hansliss/HexKeyboard/Sketch/HexKeyboard/KeyboardLib.cpp

#include <HID.h>
#include <string.h>
#include "KeyboardLib.h"

const uint8_t REPORT_ID = 0x02;
/*
static const uint8_t hidReportDescriptor[] PROGMEM = {

  //  Keyboard
  0x05, 0x01,                    // USAGE_PAGE (Generic Desktop)
  0x09, 0x06,                    // USAGE (Keyboard)
  0xa1, 0x01,                    // COLLECTION (Application)
  0x85, REPORT_ID,               //   REPORT_ID (2)
  0x05, 0x07,                    //   USAGE_PAGE (Keyboard)

  0x19, 0xe0,                    //   USAGE_MINIMUM (Keyboard LeftControl)
  0x29, 0xe7,                    //   USAGE_MAXIMUM (Keyboard RightGUI)
  0x15, 0x00,                    //   LOGICAL_MINIMUM (0)
  0x25, 0x01,                    //   LOGICAL_MAXIMUM (1)
  0x75, 0x01,                    //   REPORT_SIZE (1)

  0x95, 0x08,                      //   REPORT_COUNT (8)
  0x81, 0x02,                    //   INPUT (Data,Var,Abs)
  0x95, 0x01,                    //   REPORT_COUNT (1)
  0x75, 0x08,                    //   REPORT_SIZE (8)
  0x81, 0x03,                    //   INPUT (Cnst,Var,Abs)

  0x95, 0x06,                      //   REPORT_COUNT (6)
  0x75, 0x08,                    //   REPORT_SIZE (8)
  0x15, 0x00,                    //   LOGICAL_MINIMUM (0)
  0x25, 0x65,                    //   LOGICAL_MAXIMUM (101)
  0x05, 0x07,                    //   USAGE_PAGE (Keyboard)

  0x19, 0x00,                      //   USAGE_MINIMUM (Reserved (no event indicated))
  0x29, 0x65,                    //   USAGE_MAXIMUM (Keyboard Application)
  0x81, 0x00,                    //   INPUT (Data,Ary,Abs)
  0xc0,                          // END_COLLECTION

};
*/
static const uint8_t hidReportDescriptor[] PROGMEM = {

  //  Keyboard
  0x05, 0x01,                    // USAGE_PAGE (Generic Desktop)
  0x09, 0x06,                    // USAGE (Keyboard)
  0xa1, 0x01,                    // COLLECTION (Application)
  0x85, REPORT_ID,               //   REPORT_ID (2)
  0x05, 0x07,                    //   USAGE_PAGE (Keyboard)

// Modifiers
  0x19, 0xe0,                    //   USAGE_MINIMUM (Keyboard LeftControl)
  0x29, 0xe7,                    //   USAGE_MAXIMUM (Keyboard RightGUI)
  0x15, 0x00,                    //   LOGICAL_MINIMUM (0)
  0x25, 0x01,                    //   LOGICAL_MAXIMUM (1)
  0x75, 0x01,                    //   REPORT_SIZE (1)
  0x95, 0x08,                    //   REPORT_COUNT (8)
  0x81, 0x02,                    //   INPUT (Data,Var,Abs)

// Reserved byte
  0x95, 0x01,                    //   REPORT_COUNT (1)
  0x75, 0x08,                    //   REPORT_SIZE (8)
  0x81, 0x03,                    //   INPUT (Cnst,Var,Abs)

// Keycodes
  0x95, 0x06,                    //   REPORT_COUNT (6)
  0x75, 0x08,                    //   REPORT_SIZE (8)
  0x15, 0x00,                    //   LOGICAL_MINIMUM (0)
  0x25, 0xff,                    //   LOGICAL_MAXIMUM (df)
  0x05, 0x07,                    //   USAGE_PAGE (Keyboard)
  0x19, 0x00,                    //   USAGE_MINIMUM (Reserved (no event indicated))
  0x29, 0xff,                    //   USAGE_MAXIMUM (Keyboard Application)
  0x81, 0x00,                    //   INPUT (Data,Ary,Abs)
  
  0xc0,                          // END_COLLECTION

};
/*
char ReportDescriptor[] = {
0x05, 0x01,                         // Usage Page (Generic Desktop)
0x09, 0x06,                         // Usage (Keyboard)
0xA1, 0x01,                         // Collection (Application)
0x85, REPORT_ID,               //   REPORT_ID (2)
0x05, 0x07,                         //     Usage Page (Key Codes)
0x19, 0xe0,                         //     Usage Minimum (224)
0x29, 0xe7,                         //     Usage Maximum (231)
0x15, 0x00,                         //     Logical Minimum (0)
0x25, 0x01,                         //     Logical Maximum (1)
0x75, 0x01,                         //     Report Size (1)
0x95, 0x08,                         //     Report Count (8)
0x81, 0x02,                         //     Input (Data, Variable, Absolute)

0x95, 0x01,                         //     Report Count (1)
0x75, 0x08,                         //     Report Size (8)
0x81, 0x01,                         //     Input (Constant) reserved byte(1)

0x95, 0x05,                         //     Report Count (5)
0x75, 0x01,                         //     Report Size (1)
0x05, 0x08,                         //     Usage Page (Page# for LEDs)
0x19, 0x01,                         //     Usage Minimum (1)
0x29, 0x05,                         //     Usage Maximum (5)
0x91, 0x02,                         //     Output (Data, Variable, Absolute), Led report
0x95, 0x01,                         //     Report Count (1)
0x75, 0x03,                         //     Report Size (3)
0x91, 0x01,                         //     Output (Data, Variable, Absolute), Led report padding

0x95, 0x06,                         //     Report Count (6)
0x75, 0x08,                         //     Report Size (8)
0x15, 0x00,                         //     Logical Minimum (0)
0x25, 0x65,                         //     Logical Maximum (101)
0x05, 0x07,                         //     Usage Page (Key codes)
0x19, 0x00,                         //     Usage Minimum (0)
0x29, 0x65,                         //     Usage Maximum (101)
0x81, 0x00,                         //     Input (Data, Array) Key array(6 bytes)


0x09, 0x05,                         //     Usage (Vendor Defined)
0x15, 0x00,                         //     Logical Minimum (0)
0x26, 0xFF, 0x00,                   //     Logical Maximum (255)
0x75, 0x08,                         //     Report Count (2)
0x95, 0x02,                         //     Report Size (8 bit)
0xB1, 0x02,                         //     Feature (Data, Variable, Absolute)

0xC0                                // End Collection (Application)
};
*/
typedef struct
{
  uint8_t modifiers;
  uint8_t reserved;
  uint8_t keys[6];
} KeyReport;

void initHID() {
  static HIDSubDescriptor node(hidReportDescriptor, sizeof(hidReportDescriptor));
  //static HIDSubDescriptor node(ReportDescriptor, sizeof(ReportDescriptor));
  HID().AppendDescriptor(&node);
}

void sendKeyBuffer(uint8_t meta, uint8_t keys[]) {
  KeyReport report;

  report.modifiers = meta;
  
  for(byte b=0; b<6; ++b){
    report.keys[b] = keys[b];
  }

  HID().SendReport(REPORT_ID, &report, sizeof(report));
}
